kyledenobel/RGA_Boards/phase90/JFET characterization/jfet characterization.xlsx

JFET number | Idss (mA) | Vgs1 | Rgs1 | Beta | Vto | Idss/4 (mA) | Vin (mV) | Vout (mV) | Rdson
1 | 8.3 | -13.516375 | 715 | 4.058878185e-06 | 1.43 | 2.075 |  |  | #DIV/0!
2 | 10 | -13.29 | 684 | 5.343524503e-06 | 1.368 | 2.5 |  |  | #DIV/0!
3 | 9.2 | -13.3785 | 705 | 4.627533826e-06 | 1.41 | 2.3 |  |  | #DIV/0!
4 | 9.1 | -13.396125 | 705 | 4.577234546e-06 | 1.41 | 2.275 |  |  | #DIV/0!
5 | 8.5 | -13.480625 | 715 | 4.156682478e-06 | 1.43 | 2.125 | 188 | 46 | 165.2112676
6 | 8.3 | -13.499775 | 723 | 3.969552101e-06 | 1.446 | 2.075 | 188 | 47 | 170
7 | 8.5 | -13.463625 | 723 | 4.065203958e-06 | 1.446 | 2.125 |  |  | #DIV/0!
8 | 7.25 | -13.666 | 736 | 3.345972649e-06 | 1.472 | 1.8125 |  |  | #DIV/0!
9 | 7.6 | -13.6282 | 722 | 3.644846187e-06 | 1.444 | 1.9 |  |  | #DIV/0!
10 | 8.8 | -13.4688 | 696 | 4.541551064e-06 | 1.392 | 2.2 |  |  | #DIV/0!
11 | 8.45 | -13.4980125 | 711 | 4.17885706e-06 | 1.422 | 2.1125 |  |  | #DIV/0!
12 | 8.6 | -13.4563 | 718 | 4.170513885e-06 | 1.436 | 2.15 |  |  | #DIV/0!
13 | 8.9 | -13.4336 | 704 | 4.489362732e-06 | 1.408 | 2.225 | 188 | 46 | 165.2112676
14 | 9.9 | -13.299675 | 687 | 5.243988482e-06 | 1.374 | 2.475 |  |  | #DIV/0!
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
