kyledenobel/RGA_Boards/Overdrive/sim/Draft2.asc

R1: res; 22k
R2: res; 100k
R3: res; 10k
V1: voltage; 0.5
Named nets: 0, Vo, Vp
