kyledenobel/RGA_Boards/Overdrive/sim/Draft1.asc

C1: cap; 1µ
L1: ind; 1m; Rser=1m
R1: res; 1
V1: voltage; 9
Named nets: in, out
.tran 0 0.4 0 0.0001
