kyledenobel/RGA_Boards/Overdrive/sim/Overdrive.asc

C1: cap; 10µ
C2: cap; 10µ
C3: cap; 10n
C4: cap; 1µ
C5: cap; 1µ
C_B: cap; 1µ
C_E: cap; 100µ
D1: diode
D2: diode
Q1: npn
Q2: npn
R1: res; 130k
R2: res; 18k
R3: res; 110k
R4: res; 36k
R5: res; 10k
R6: res; 100k
R7: res; 1k
R8: res; 1k
R9: res; 1k
R_C: res; 6.2k
R_E1: res; 100
R_E2: res; 1k
R_L: res; 10k
U1: opamp
U2: opamp
U3: opamp
V1: voltage; 15
V2: voltage; SINE(0 0.5 1000); AC 0.5 0
Named nets: 0, VCC, out, input, cascode
.ac dec 50 100 20000
.lib opamp.sub
.tran 0 1 0 0.0001
